gyuha/my-keyboard/.forge/done/260812-024711-magnet-pocket-depth-for-glue/STATUS.md

# STATUS — 자석 포켓 깊이를 접착제 부착 기준(2.2mm)으로 교정
slug: magnet-pocket-depth-for-glue
status: done
executed: 2026-08-12
completed: 2026-08-12
verified: yes (verify_magnet_pockets.py → 22개 검사 PASS, exit 0; 실측 깊이 2.2000mm / 뒷벽 잠여 3.8000mm)
retro: skipped (사용자가 회고를 건너뛰고 봉인 선택 — 학습은 run.md에 남고, 승격은 이후 fg-learn으로 유보)
docs updated: .forge/CONTEXT.md — 자석 포켓 · 결합면
