gyuha/my-keyboard/.forge/branch/add-function/STATUS.md

# STATUS — DXF 스위치 레이아웃으로 3D 프린팅용 분할 키보드 풀 케이스
slug: freecad-keyboard-case
status: executed
executed: 2026-07-05
verified: yes (freecadcmd build_assembly, 뒷벽 부품배치 조정 후 재검증 → 반쪽당 2부품 plate/body-tub 전부 isValid, body_solids=1·plate_solids=1, 상판 나사홀 screw_bad=0, TRRS 모서리서 20mm·보드↔TRRS 10mm 간격, 조립 간섭 0.000, 풋프린트 좌148.2×129.3·우195.8×129.3 ≤220, 4 STL + keyboard.FCStd 갱신)
retro: pending
