gyuha/my-keyboard/.forge/branch/feature/20260919-pcb-body/done/260824-003015-pcb-align-1of4/run.md

# run — epro 파서와 PCB 정합 검증기

## 슬라이스별 결과

- S1 `tools/pcb.py` 로더(zip + 줄 단위 JSON), 보드 4장 식별 — ⚠ 계획은 "project.json 의 이름으로 식별"이었으나 이름(`PCB13` 등)이 뜻을 갖지 않아 **디자이너 접두어(`LEFT*`/`RIGHT*`)로 좌/우를, 스위치 유무로 main/aux 를 판정**하는 의미 기반 접근자(`main(side)`/`aux(side)`)를 함께 넣었다. 이름 키(`boards`)도 유지해 계획의 완료 기준(63/90/3/3)은 그대로 검사한다.
- S2 외곽·마운팅 홀 추출 — ✅ 계획대로. 좌 146.21×103.35 r3.00 / 우 198.60×103.35 r3.00, 홀 ⌀3.55 4개가 양쪽 다 가장자리 3.0mm 인셋.
- S3 핀맵 추출 — ✅ 계획대로. `ROW0~4=GP2~GP6`, `COL0~8=GP7~GP15`, `TX0=GP0`, `RX0=GP1`, 좌측은 COL6 까지.
- S4 매트릭스 추출 — ✅ 계획대로. 좌 30키 `[7,6,6,6,5]` / 우 43키 `[9,9,8,9,8]`, 실크 라벨까지 일치.
- S5 `tools/verify_pcb_matrix.py` — ✅ 계획대로. 우 row0/row2/row4 를 각각 한 줄로 지목하고 exit 1.
- S6 aux 보드 배치 확정 — ⚠ **좌우가 비대칭이라는 사실이 새로 드러났다.** 좌측은 계획이 예상한 대로 후면 오버행 `+1.66mm`인데, **우측은 `-16.30mm`(후면에서 16.3mm 안쪽)** 이다.

## Plan vs actual

계획한 6개 슬라이스가 전부 들어갔고 Non-goals(어긋남을 고치지 않는다 / FreeCAD·README·PARAMS 를 건드리지 않는다 / uf2 를 갱신하지 않는다)를 지켰다. 워크플로우는 쓰지 않았다 — 슬라이스 6개가 모두 같은 두 파일에 직렬 의존해 병렬 서브에이전트가 서로를 덮어쓸 구조였고, fg-run 의 "규모가 작으면 직접 처리가 싸고 빠르다" 원칙에 해당했다.

TDD 로 진행했다. `tools/test_pcb.py` 를 먼저 쓰고 `ModuleNotFoundError` 로 적색을 확인한 뒤 구현했다. 테스트 실행 방식은 계획이 적은 `pytest` 대신 **저장소의 기존 방식**(`tools/test_gen_dxf.py` 와 같은 `failures` 리스트 + `python3 tools/test_pcb.py`)을 따랐다 — pytest 는 이 저장소에 설치돼 있지 않고 의존성을 새로 들일 이유가 없었다.

## 현장 판단

**하면 부품의 미러 축을 데이터로 확정했다.** epro 는 layer 2(하면) 부품의 풋프린트를 미러해 그리는데 그 축이 X 인지 Y 인지가 문서화돼 있지 않다. 두 가정을 다 계산해 보고, **X 축 미러(y → −y)** 만이 좌우 양쪽에서 헤더 1번 패드가 자기가 담당하는 `ROW0` 쪽(보드 상단)에 놓여 배선이 성립함을 확인했다. Y 축 미러 가정에서는 `ROW0` 배선이 보드를 가로질러야 하고, 180° 회전 가정에서는 aux 보드가 메인 PCB 밖으로 30mm 튀어나온다. 이 결론에서 두 보드는 **회전·반사 없는 순수 평행이동**으로 맞물린다.

## 다음 단계로 넘길 발견

1. **우측 aux 보드가 후면 벽에 닿지 않는다 (−16.30mm).** 3of4 의 "후면 벽 USB-C 개구부 2개"(S8)가 우측 반쪽에서는 성립하지 않는다. 좌측은 커넥터 면이 후면 가장자리와 사실상 일치하는데(+1.66mm), 우측은 헤더가 좌측보다 17.65mm 아래(y 60.20 vs 77.85)에 있고 aux 소켓 위치 차이 3.37mm 를 상쇄해도 14.28mm 가 남는다. 3of4 진입 전에 판단이 필요하다.
2. **`OuterMargin` 11.5 의 근거는 좌측 반쪽에서만 나온다.** 우측은 오버행이 없어 10.0 으로 충분하다. 등방 스칼라 하나를 쓰기로 한 결정(ADR `260824-001948`)상 11.5 가 양쪽에 적용된다.
3. **`.worktree/pcb` 스펙 문서의 마운팅 홀 기술이 틀렸음을 재확인했다.** "좌 1개, 우 없음"이 아니라 양쪽 4개다. 그 문서를 근거로 삼는 판단이 남아 있으면 폐기해야 한다.

## DoD baseline → after

1. `python3 tools/test_pcb.py` — 파일 없음 → **exit 0** (통과)
2. `python3 tools/pcb.py --outline` — 파일 없음 → **좌 `146.21 x 103.35 r3.00` / 우 `198.60 x 103.35 r3.00`**
3. `python3 tools/verify_pcb_matrix.py` — 파일 없음 → **exit 1, 불일치 6건**(우 row0·row2·row4 + 핀 3건). 이 파트에서는 exit 1 이 정상이다
4. `python3 tools/verify_keylayout.py` — exit 0 (`5행 72키`) → **exit 0 (`5행 72키`, 변화 없음)**. 회귀 방지 검사이므로 불변이 기대 결과다
