gyuha/my-keyboard/.forge/branch/feature/20260919-pcb-body/done/260824-003015-pcb-align-1of4/STATUS.md

# STATUS — epro 파서와 PCB 정합 검증기
slug: pcb-align-1of4
status: done
executed: 2026-08-24
completed: 2026-08-24
verified: yes (tools/test_pcb.py exit 0 · verify_pcb_matrix.py exit 1 로 우측 3행 불일치 지목 · verify_keylayout.py exit 0 불변)
retro: skipped (fg-next all 자동 구동 — 학습은 run.md 에 남고 승격은 이후 fg-learn 으로 미룸)
docs updated: none
