gyuha/my-keyboard/.forge/branch/feature/20260919-pcb-body/done/260824-003605-pcb-align-2of4/STATUS.md

# STATUS — 배열에 우측 6 키 추가 + 펌웨어 PCB 정합
slug: pcb-align-2of4
status: done
executed: 2026-08-24
completed: 2026-08-24
verified: yes (verify_keylayout 5행 73키 우[9,9,8,9,8] · verify_pcb_matrix exit 0 · qmk compile exit 0 · uf2 645b3be2 로 갱신 · 생성 DXF 가 PCB 좌표와 최대 편차 0.056mm)
retro: skipped (fg-next all 자동 구동 — 학습은 run.md 에 남고 승격은 이후 fg-learn 으로 미룸)
docs updated: none
