gyuha/my-keyboard/.forge/branch/feature/20260919-pcb-body/done/260824-005111-pcb-align-3of4/STATUS.md

# STATUS — 케이스 PCB 정합 + 바디 높이 14mm
slug: pcb-align-3of4
status: done
executed: 2026-08-24
completed: 2026-08-24
verified: yes (외곽 좌 156.06x113.95x14.00 / 우 208.45x113.95x14.00 · verify_no_support exit 0 · verify_magnet_pockets exit 0 (⌀8) · 나사가 PCB 홀과 편차 0.004mm · PCB 참조 상면 z=-1.00 · STL 8종 재export · 파트 색상 12개 유지)
retro: skipped (fg-next all 자동 구동 — 학습은 run.md 에 남고 승격은 이후 fg-learn 으로 미룸)
docs updated: none
