gyuha/my-keyboard/.forge/branch/feature/20260919-pcb-body/done/260824-005416-pcb-align-4of4/STATUS.md

# STATUS — 문서를 PCB 기준으로 다시 쓰기
slug: pcb-align-4of4
status: done
executed: 2026-08-24
completed: 2026-08-24
verified: yes (DoD 6항목 전부 충족 — 핀 표 PCB 기준 재작성·TRRS 0·배선도 참조 0·kbfirmware 0·부품 표 갱신·매트릭스 표 생성기 재현 가능. verify_keylayout·verify_pcb_matrix·test_pcb 회귀 없음)
retro: skipped (fg-next all 자동 구동 — 학습은 run.md 에 남고 승격은 이후 fg-learn 으로 미룸)
docs updated: none
