gyuha/my-keyboard/.forge/branch/feature/new-60percent/done/260821-211737-freecad-5row-dxf-generator-1of2/STATUS.md

# STATUS — KLE에서 DXF를 생성해 배열 원천을 하나로 만든다 (part 1/2)
slug: freecad-5row-dxf-generator-1of2
status: done
executed: 2026-08-21
completed: 2026-08-21
verified: yes (test_gen_dxf.py exit 0 — 원본 6행 DXF 대조 편차 0.0006mm; 5행 DXF 좌 30+4 / 우 42+6)
retro: .forge/branch/feature/new-60percent/retro/260821-233844-freecad-5row-dxf-generator-1of2.md (일괄 승급 2026-08-21)
docs updated: none (승급 보류)
