gyuha/my-keyboard/.forge/branch/feature/260705-freecad/done/2026-07-05-keyboard-plate-rear-mount-lower/STATUS.md

# STATUS — keyboard-plate 뒷쪽 부품 받침 낮추기 + 노출 홀 위치 연동 조정
slug: keyboard-plate-rear-mount-lower
status: done
executed: 2026-07-05
completed: 2026-07-05
verified: yes (좌우 body 부품받침 z=4mm, 포트홀 중심 z=7mm 측정 확인; 뒷변 받침 재구성은 대상 구조 부재로 실행 중 skip 승인됨; STL 재출력 git 커밋 ff6f291로 확인)
retro: .forge/retro/2026-07-05-keyboard-plate-rear-mount-lower.md
docs updated: ADR-0001 개정 (2026-07-05), CONTEXT.md 변경 없음
