gyuha/my-keyboard/.forge/branch/feature/260705-freecad/done/2026-07-07-rp2040-zero-split-firmware/STATUS.md

# STATUS — RP2040-Zero 분할 키보드 QMK 펌웨어 포팅 (VIA 포함)
slug: rp2040-zero-split-firmware
status: done
executed: 2026-07-05
completed: 2026-07-07
verified: yes (qmk compile -kb gkey -km default 실제 실행해 성공 확인, .uf2 생성; 실물 하드웨어 플래싱·키입력 확인은 사용자 몫)
retro: skipped (이미 executed·verified: yes 상태로 장기 대기 중이던 작업; 새 FreeCAD plate 작업을 위해 슬롯을 비우려 회고 생략 봉인 (사용자 결정))
docs updated: none
