gyuha/my-keyboard/.forge/branch/feature/260705-freecad/done/2026-07-12-left-body-usb-seat-removal/STATUS.md

# STATUS — 좌측 바디에서 컨트롤러 시트·USB 홀 제거
slug: left-body-usb-seat-removal
status: done
executed: 2026-07-12
completed: 2026-07-12
verified: yes (기하 프로브 전 항목 통과 — 구 USB 홀 180/180·구 시트 522.24/522.24 솔리드, 잭 홀·뒷막이 유지, 우측 부피 무변화, 좌측 참조객체 부재, STL 재생성)
retro: skipped (fg-next all 자동 진행 — 학습은 run.md, 승급은 추후 fg-learn)
docs updated: none
