gyuha/my-keyboard/.forge/branch/feature/260705-freecad/STATUS.md

# STATUS — Fn+Command 왼쪽 Alt↔Command 스왑 토글
slug: fn-cmd-win-mac-swap
status: executed
executed: 2026-07-13
verified: pending
retro: pending
