gyuha/my-keyboard/.forge/branch/feature/20260919-pcb-body/done/260824-004128-split-master-left/STATUS.md

# STATUS — PC 연결 반쪽을 좌측으로 (MASTER_LEFT)
slug: split-master-left
status: done
executed: 2026-08-24
completed: 2026-08-24
verified: yes (MASTER_LEFT 1 / MASTER_RIGHT 0 · qmk compile exit 0 · verify_pcb_matrix·verify_keylayout exit 0 · uf2 d14c6898 로 갱신)
retro: skipped (fg-next all 자동 구동 — 학습은 run.md 에 남고 승격은 이후 fg-learn 으로 미룸)
docs updated: ADR 260824-003937-usb-host-is-the-left-half
