gyuha/my-keyboard/.forge/branch/feature/new-60percent/done/260821-212613-freecad-5row-regenerate-model-2of2/STATUS.md

# STATUS — 5행 DXF로 FreeCAD 모델과 출력 STL을 재생성한다 (part 2/2)
slug: freecad-5row-regenerate-model-2of2
status: done
executed: 2026-08-21
completed: 2026-08-21
verified: yes (verify_no_support.py exit 0 + verify_magnet_pockets PASS 22/FAIL 0; 8개 파트 valid solids, 컷아웃 좌 30+4 / 우 42+6, 플레이트 y −23.81mm)
retro: .forge/branch/feature/new-60percent/retro/260821-233845-freecad-5row-regenerate-model-2of2.md (일괄 승급 2026-08-21)
docs updated: none (승급 보류)
