gyuha/my-keyboard/.forge/branch/feature/new-60percent/done/260821-195931-keylayout-drop-function-row/STATUS.md

# STATUS — 펑션 행을 없앤 5행 65% 배열
slug: keylayout-drop-function-row
status: done
executed: 2026-08-21
completed: 2026-08-21
verified: yes (verify_keylayout.py exit 0 + qmk compile exit 0; 5행 실물 없어 타이핑 검증 불가)
retro: /Users/gyuha/workspace/my-keyboard/.forge/branch/feature/new-60percent/retro/260821-195742-keylayout-drop-function-row.md
docs updated: ADR 260821-171944 개정 (원천 6곳 · DXF 누락 보완)
