gyuha/my-keyboard/.forge/branch/feature/260705-freecad/done/2026-07-12-rp2040-zero-split-firmware/STATUS.md

# STATUS — RP2040-Zero 분할 키보드 QMK 펌웨어 포팅 (VIA 포함)
slug: rp2040-zero-split-firmware
status: done
executed: 2026-07-11
completed: 2026-07-12
verified: yes (재실행 UAT — S1~S4 완료 기준 정적 재검증 통과 + qmk compile -kb gkey -km default 성공, gkey_default.uf2 84,480B 재생성; 실물 플래싱·키입력 확인은 사용자 몫)
retro: skipped (의도적 재실행으로 코드 변경 0건·괴리 사실상 없음 — task #3 실행을 위해 슬롯을 비우며 회고 생략 (사용자 결정))
docs updated: none
