gyuha/my-keyboard/image/pcb/left-bottom.png

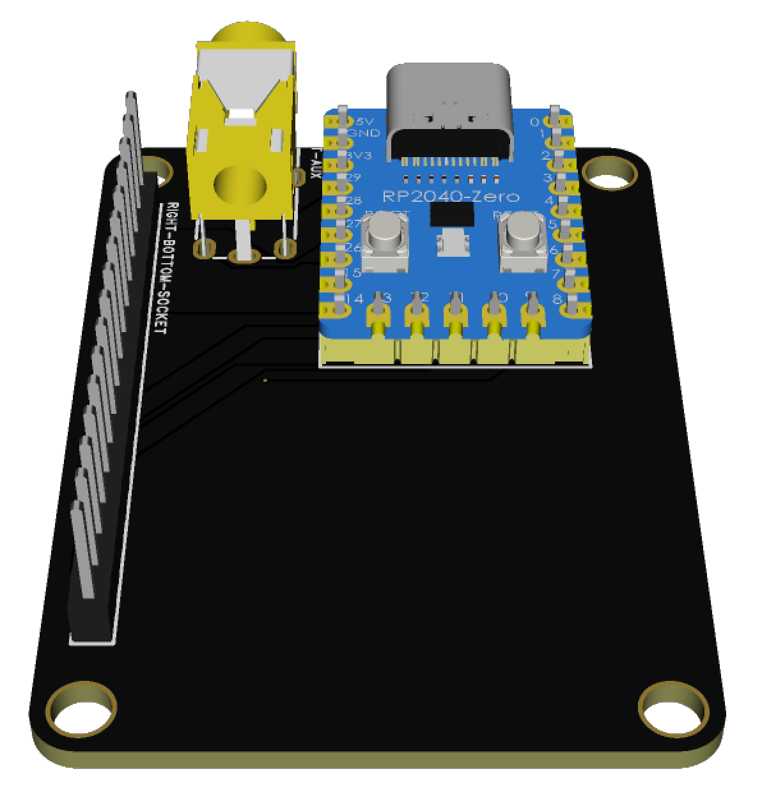
image/pcb/left-bottom.png
