gyuha/my-keyboard/image/pcb/left-top.png

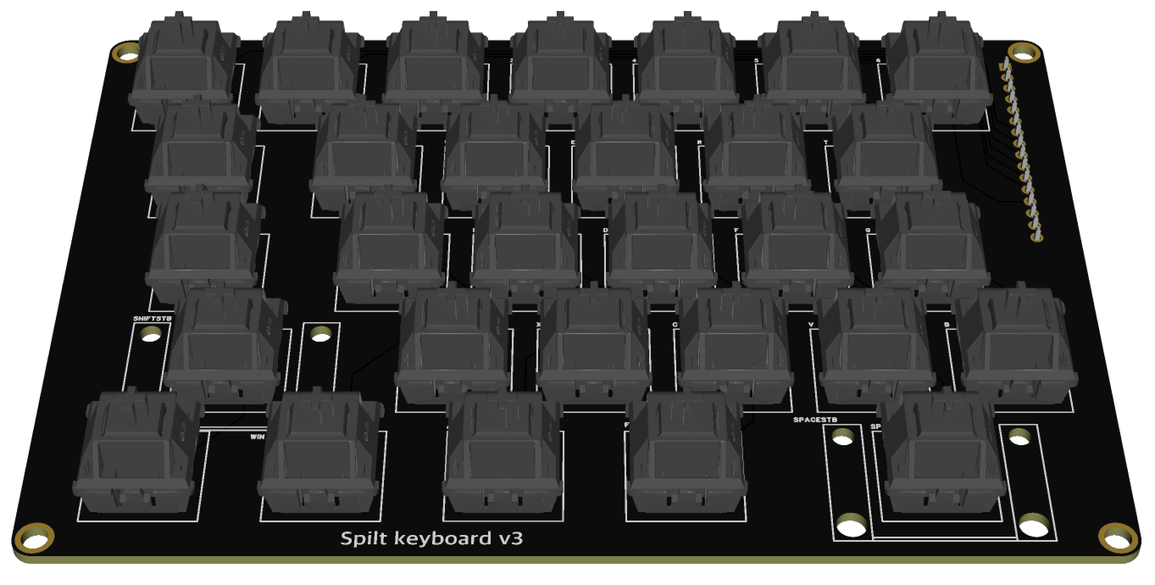
image/pcb/left-top.png
