gyuha/my-keyboard/image/pcb/right-top.png

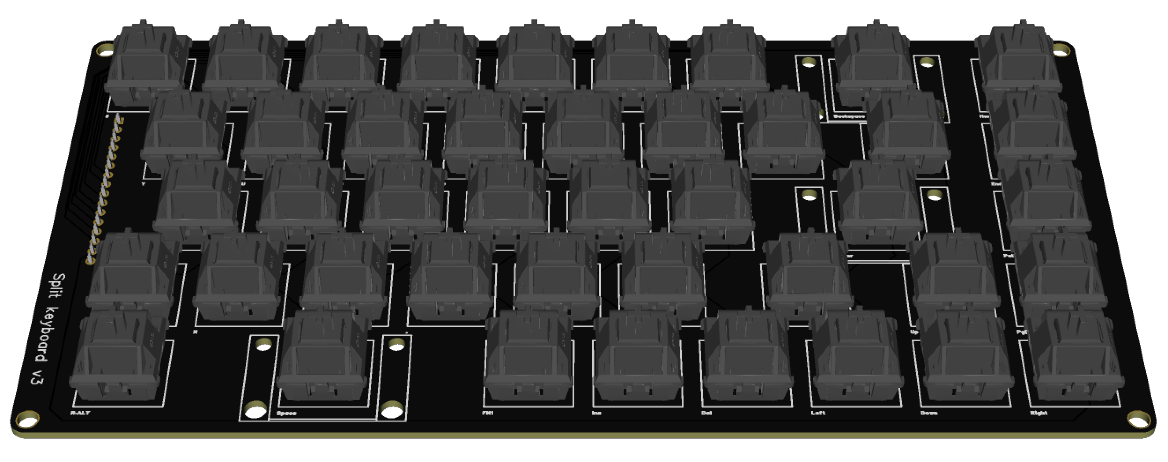
image/pcb/right-top.png
