gyuha/my-keyboard/image/stero connect ping.png

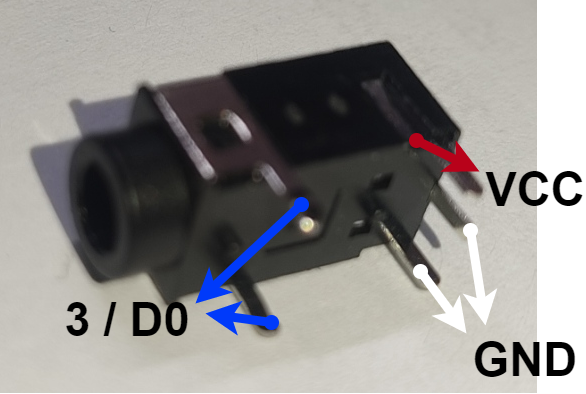
image/stero connect ping.png
