gyuha/my-keyboard/image/summary.png

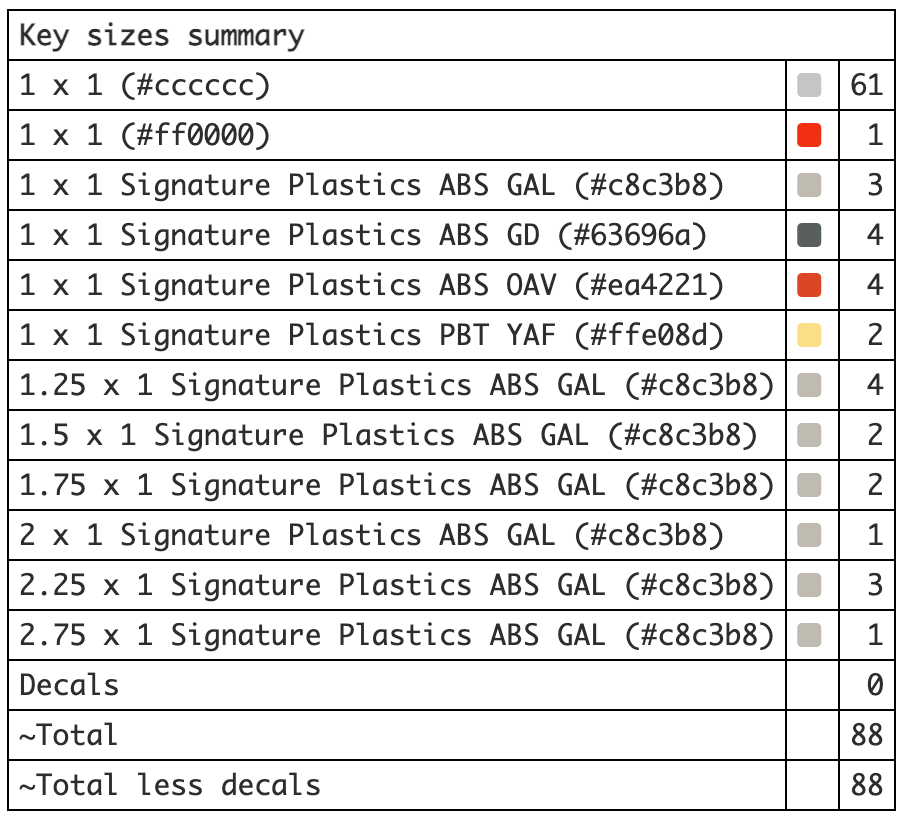
image/summary.png
