gyuha/my-keyboard/freecad/parametric_stl/right_switch_plate.stl

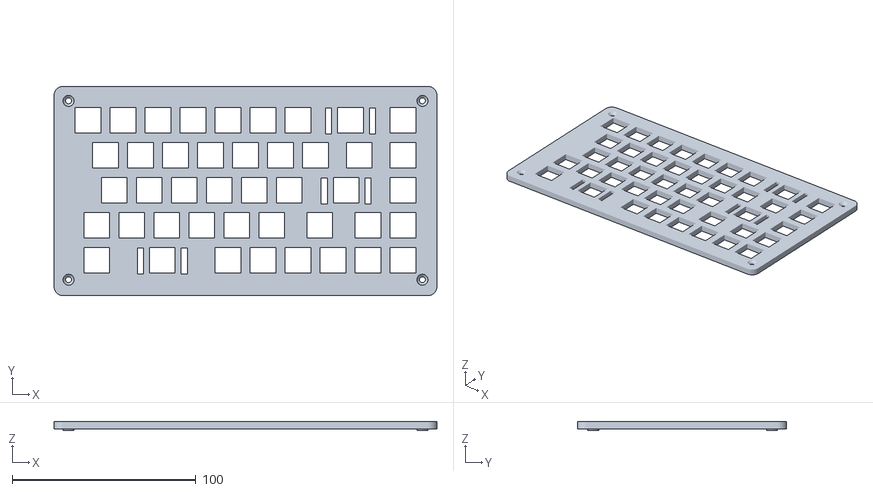
[picture p26: CAD file, 2026-08-24]
freecad/parametric_stl/right_switch_plate.stl
208.4 x 114.0 x 5.00
