gyuha/my-keyboard/freecad/parametric_stl/left_switch_plate.stl

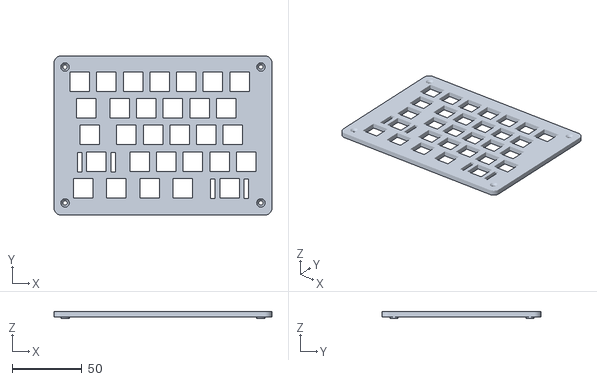
[picture p27: CAD file, 2026-08-24]
freecad/parametric_stl/left_switch_plate.stl
156.1 x 114.0 x 5.00
